pa3gsb/Radioberry-2.x-extensions/Radioberry_LPF_V1.3/Radioberry_LPF_V1.3/3D_ models/WE_7845.stp

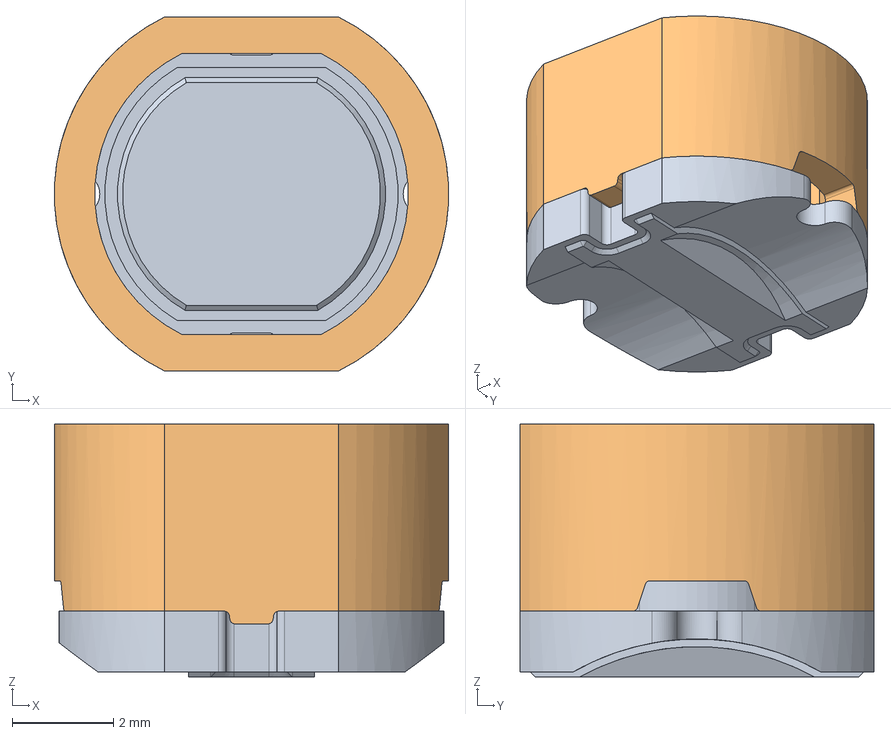
[picture p23: CAD file, 2020-11-24]
Radioberry_LPF_V1.3/Radioberry_LPF_V1.3/3D_ models/WE_7845.stp
7.79 x 7.00 x 5.00 mm
