pa3gsb/Radioberry-2.x-extensions/Radioberry-PA-20W/3D_Models/CAP2200_n.STEP

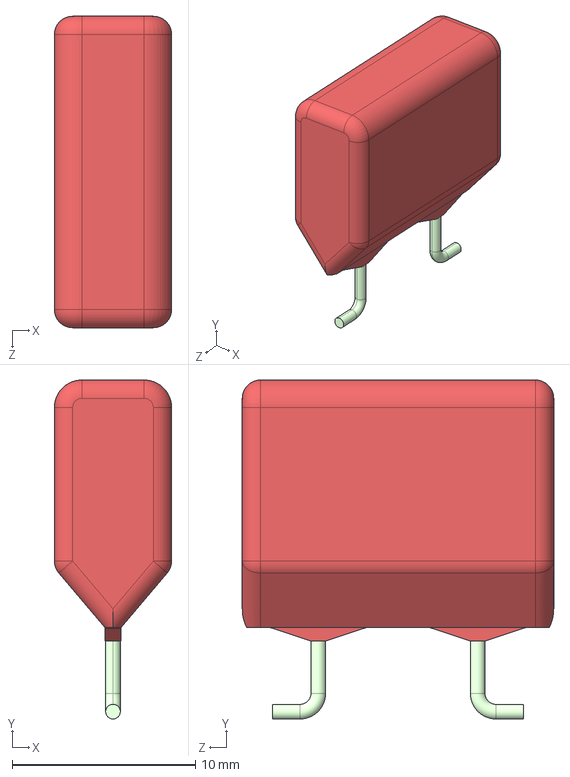
[picture p24: CAD file, 2020-11-24]
Radioberry-PA-20W/3D_Models/CAP2200_n.STEP
6.40 x 18.5 x 17.0 mm
