pa3gsb/Radioberry-2.x-extensions/Radioberry_LPF_V1.3/Radioberry_LPF_V1.3/3D_ models/AGQ_(GQ)_Relays.STEP

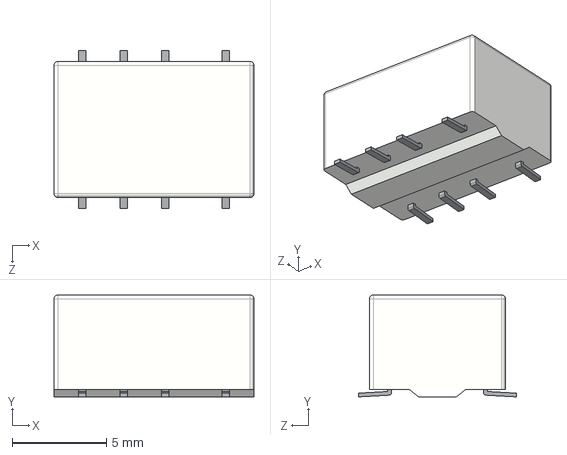
[picture p25: CAD file, 2020-11-24]
Radioberry_LPF_V1.3/Radioberry_LPF_V1.3/3D_ models/AGQ_(GQ)_Relays.STEP
10.6 x 5.40 x 8.40 mm
