pa3gsb/Radioberry-2.x-extensions/Radioberry-PA-20W/3D_Models/PJ-063BH.step

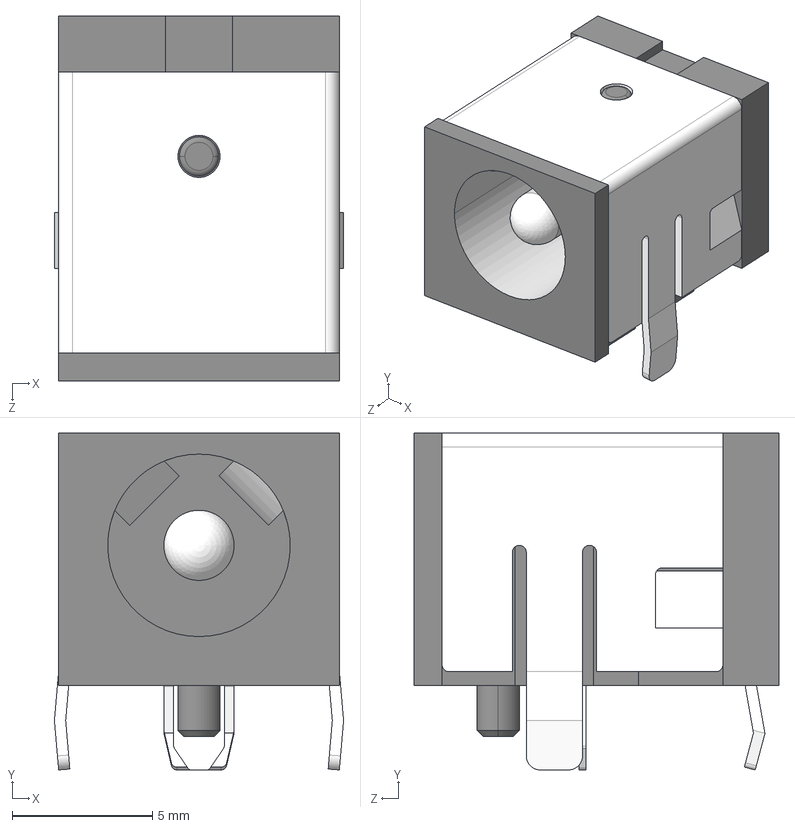
[picture p26: CAD file, 2020-11-24]
Radioberry-PA-20W/3D_Models/PJ-063BH.step
10.3 x 12.0 x 13.0 mm
