pa3gsb/Radioberry-2.x-extensions/Radioberry_LPF_V1.3/Radioberry_LPF_V1.3/3D_ models/sma1.STEP

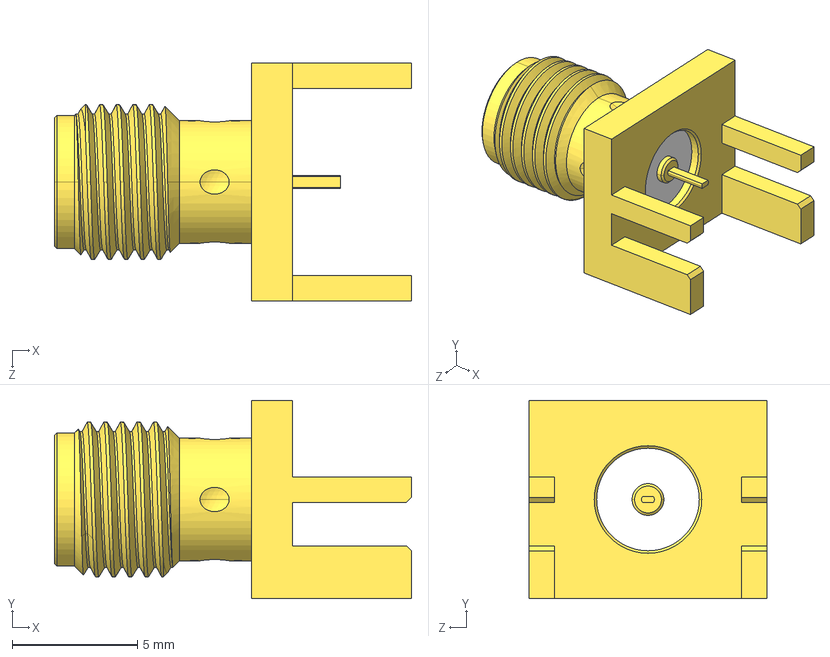
[picture p27: CAD file, 2020-11-24]
Radioberry_LPF_V1.3/Radioberry_LPF_V1.3/3D_ models/sma1.STEP
14.3 x 7.92 x 9.52 mm
