pa3gsb/Radioberry-2.x-extensions/Radioberry-PA-20W/3D_Models/CAP2200.STEP

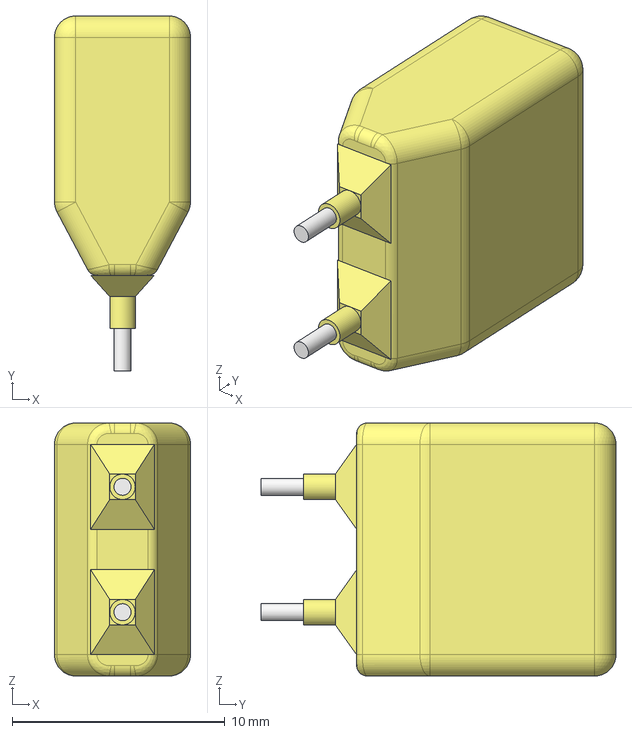
[picture p28: CAD file, 2020-11-24]
Radioberry-PA-20W/3D_Models/CAP2200.STEP
6.40 x 16.7 x 11.9 mm
