pa3gsb/Radioberry-2.x-extensions/Radioberry-PA-20W/3D_Models/SMA-J-P-H-RA-TH1.stp

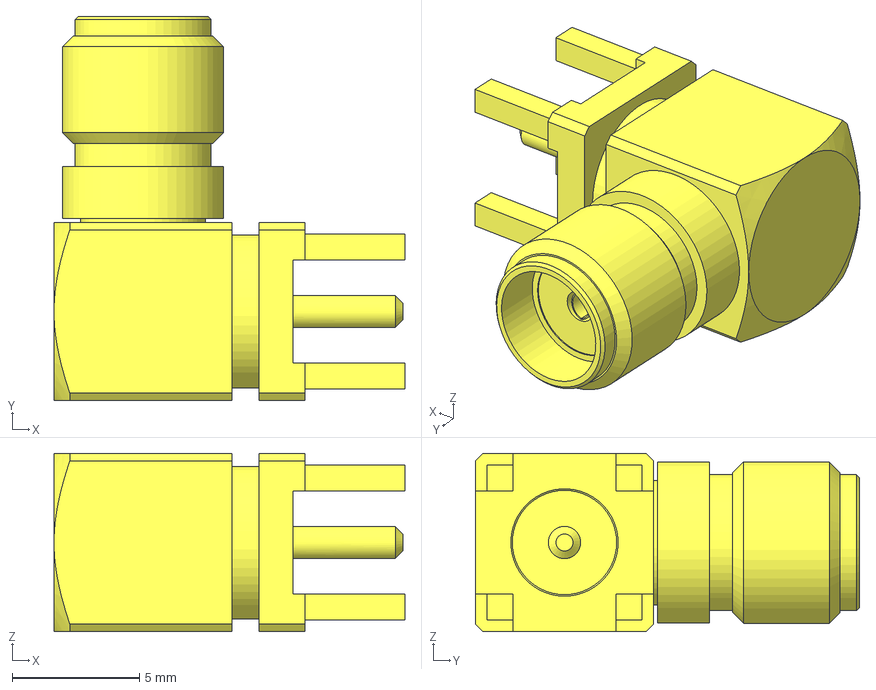
[picture p29: CAD file, 2020-04-24]
Radioberry-PA-20W/3D_Models/SMA-J-P-H-RA-TH1.stp
13.8 x 15.1 x 7.00 mm
