pa3gsb/Radioberry-2.x-extensions/Radioberry_LPF_V1.3/Radioberry_LPF_V1.3/3D_ models/SN74LVC1G34DBVR.STEP

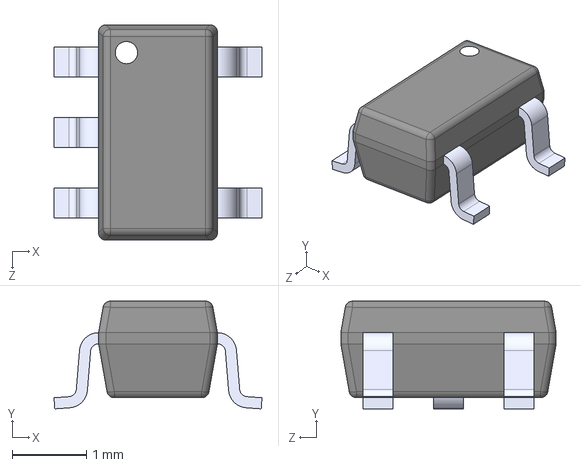
[picture p30: CAD file, 2020-11-24]
Radioberry_LPF_V1.3/Radioberry_LPF_V1.3/3D_ models/SN74LVC1G34DBVR.STEP
2.80 x 1.45 x 2.90 mm
