pa3gsb/Radioberry-2.x-extensions/Radioberry-PA-20W/3D_Models/to92SMD.STEP

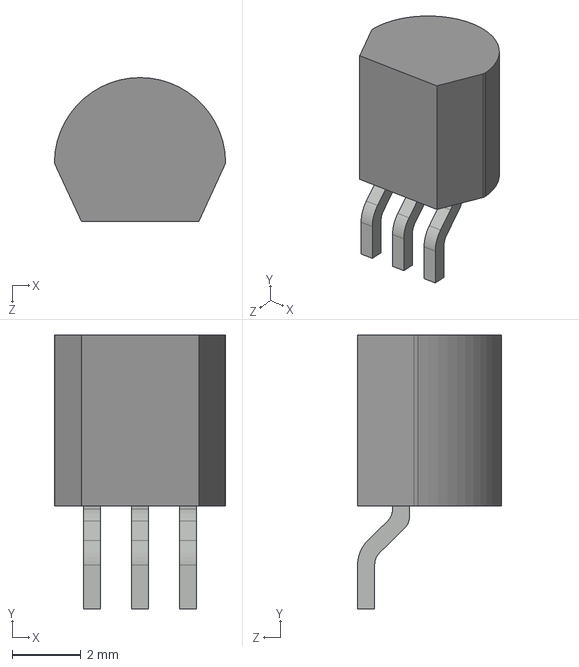
[picture p31: CAD file, 2020-04-24]
Radioberry-PA-20W/3D_Models/to92SMD.STEP
5.00 x 8.00 x 4.20 mm
TO92
to92pin x 3
