pa3gsb/Radioberry-2.x-extensions/Radioberry_LPF_V1.3/Radioberry_LPF_V1.3/3D_ models/SRP2510A.stp

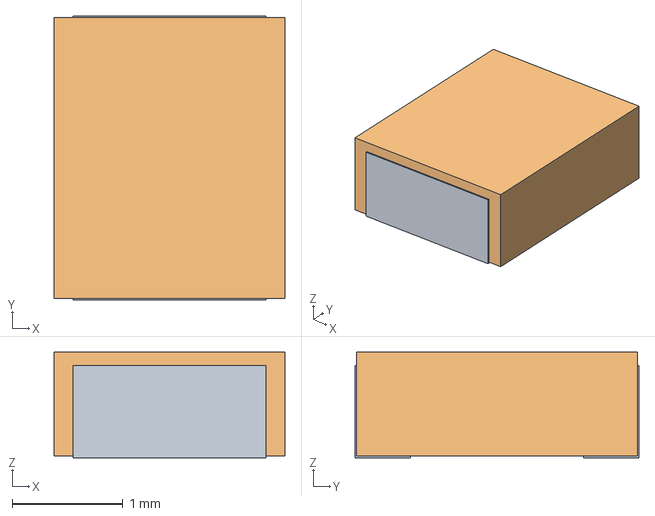
[picture p32: CAD file, 2020-11-24]
Radioberry_LPF_V1.3/Radioberry_LPF_V1.3/3D_ models/SRP2510A.stp
2.09 x 2.57 x 0.955 mm
