pa3gsb/Radioberry-2.x-extensions/Radioberry-PA-20W/3D_Models/BN43-1502.STEP

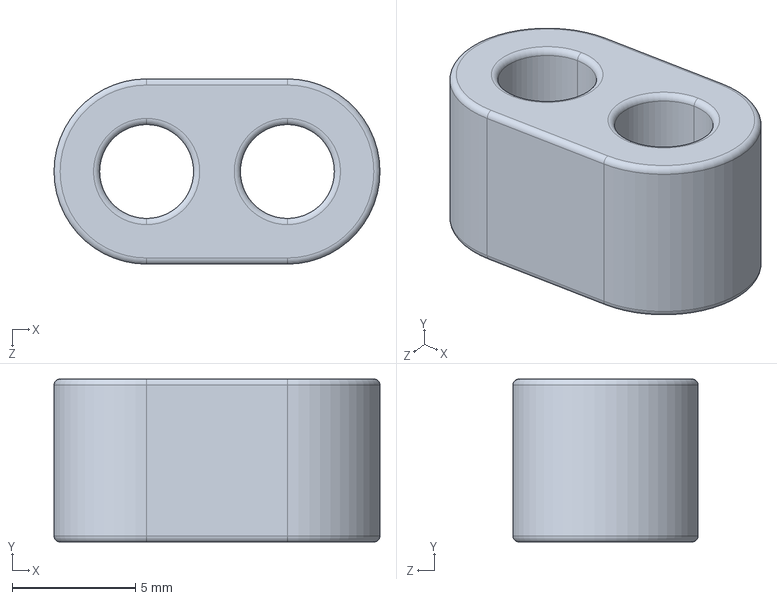
[picture p33: CAD file, 2020-04-24]
Radioberry-PA-20W/3D_Models/BN43-1502.STEP
13.2 x 6.60 x 7.50 mm
