pa3gsb/Radioberry-2.x-extensions/Radioberry-PA-20W/3D_Models/BN43-2402.STEP

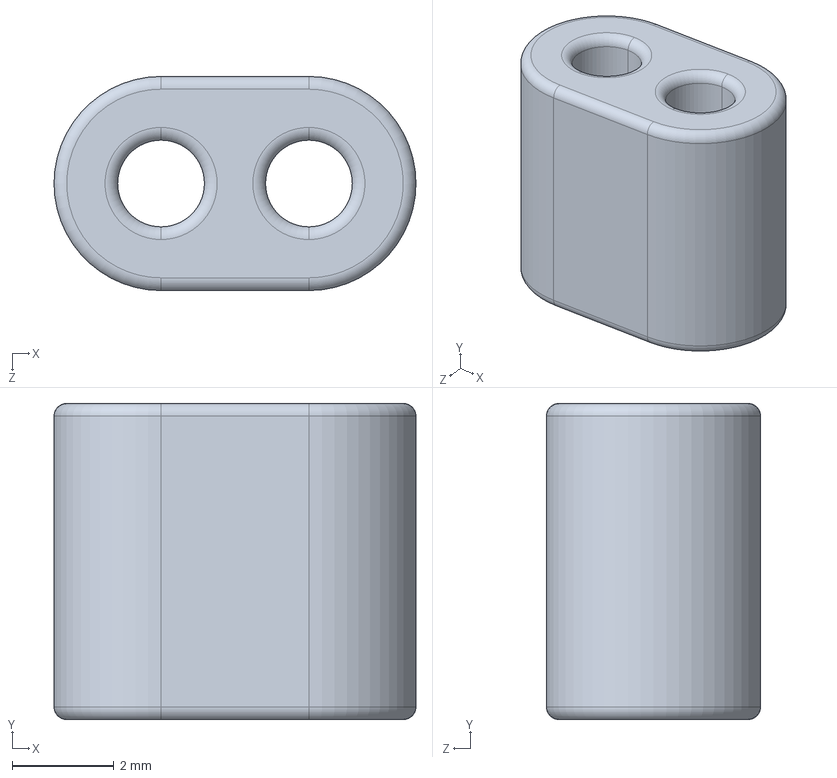
[picture p35: CAD file, 2020-04-24]
Radioberry-PA-20W/3D_Models/BN43-2402.STEP
7.10 x 6.20 x 4.20 mm
