pa3gsb/Radioberry-2.x-extensions/Radioberry-PA-20W/3D_Models/EDH106M025A9BAA.step

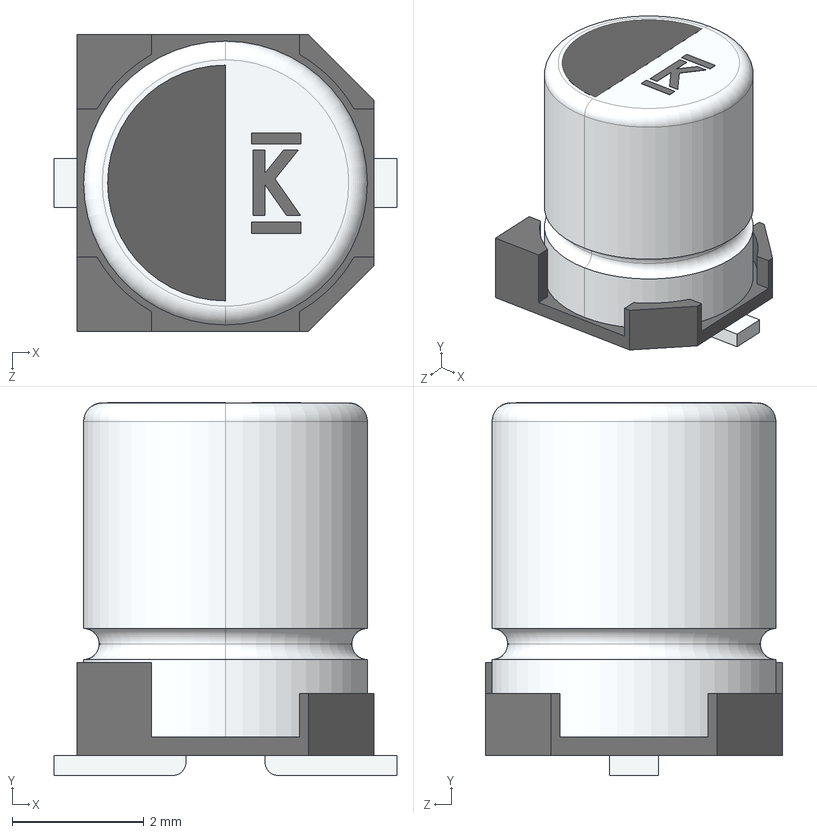
[picture p37: CAD file, 2020-04-24]
Radioberry-PA-20W/3D_Models/EDH106M025A9BAA.step
5.20 x 5.66 x 4.50 mm
