pa3gsb/Radioberry-2.x-extensions/Radioberry-PA-20W/3D_Models/BN43-202.STEP

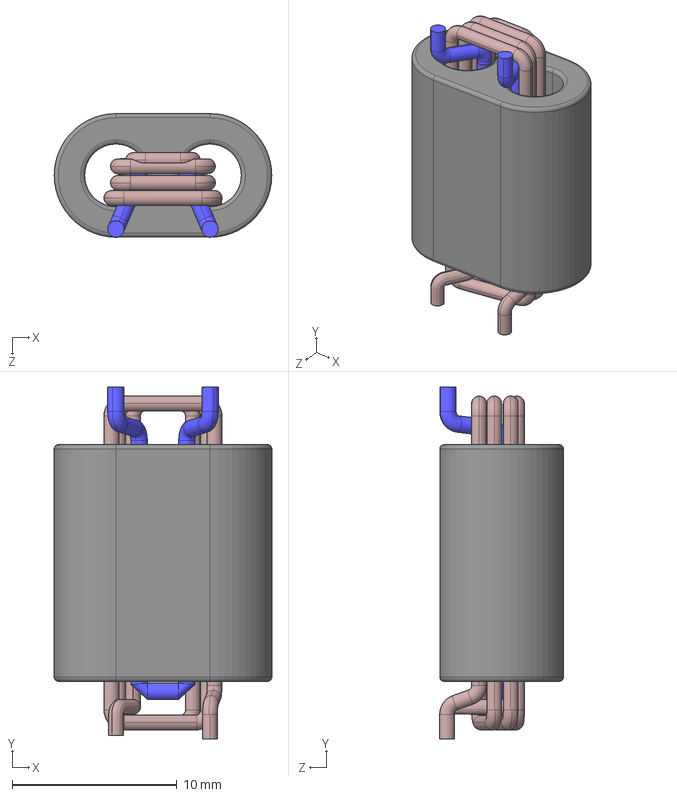
[picture p39: CAD file, 2020-04-24]
Radioberry-PA-20W/3D_Models/BN43-202.STEP
13.2 x 21.4 x 7.51 mm
BN43-202
primary
pin x 2
secondary
