pa3gsb/Radioberry-2.x-extensions/Radioberry_LPF_V1.3/Radioberry_LPF_V1.3/3D_ models/SRN6028 series.stp

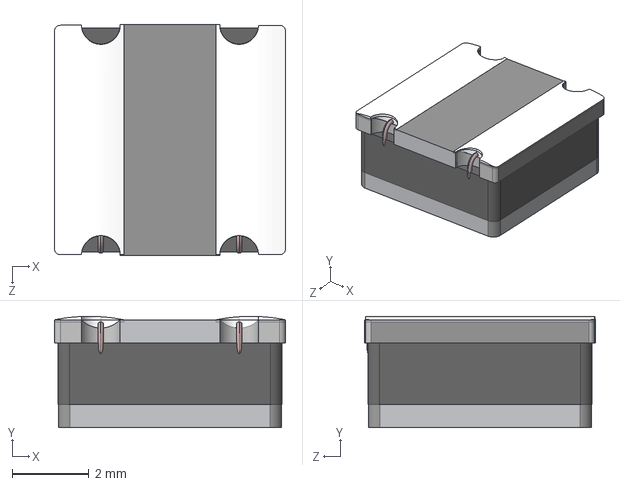
[picture p41: CAD file, 2020-11-24]
Radioberry_LPF_V1.3/Radioberry_LPF_V1.3/3D_ models/SRN6028 series.stp
6.00 x 2.89 x 6.00 mm
