pa3gsb/Radioberry-2.x-extensions/Radioberry_LPF_V1.3/Radioberry_LPF_V1.3/3D_ models/IND_NLCV32TR_TDK.step

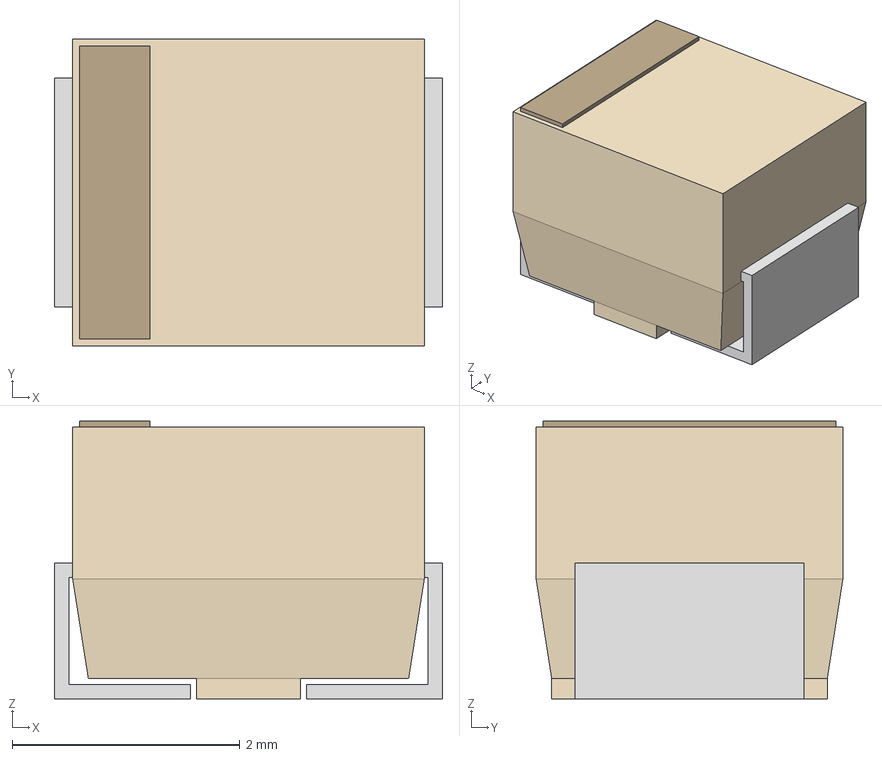
[picture p42: CAD file, 2020-11-24]
Radioberry_LPF_V1.3/Radioberry_LPF_V1.3/3D_ models/IND_NLCV32TR_TDK.step
3.40 x 2.69 x 2.44 mm
