pa3gsb/Radioberry-2.x-extensions/Radioberry_LPF_V1.3/Radioberry_LPF_V1.3/3D_ models/WE_7440450018.stp

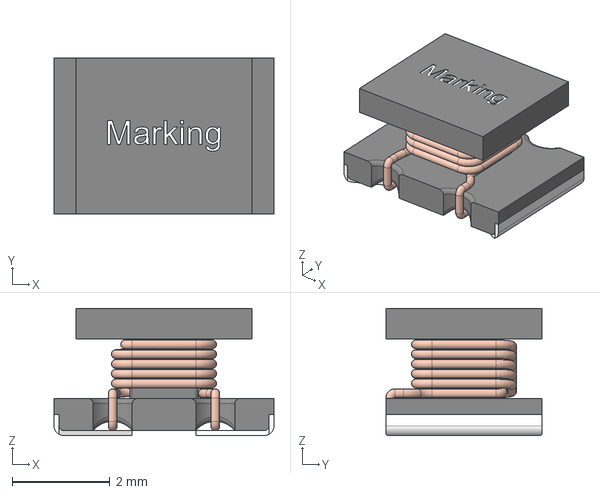
[picture p43: CAD file, 2020-11-24]
Radioberry_LPF_V1.3/Radioberry_LPF_V1.3/3D_ models/WE_7440450018.stp
4.50 x 3.20 x 2.60 mm
Kern x 2
Pin x 2
