pa3gsb/Radioberry-2.x-extensions/Radioberry_LPF_V1.3/Radioberry_LPF_V1.3/3D_ models/SRN2012 series.stp

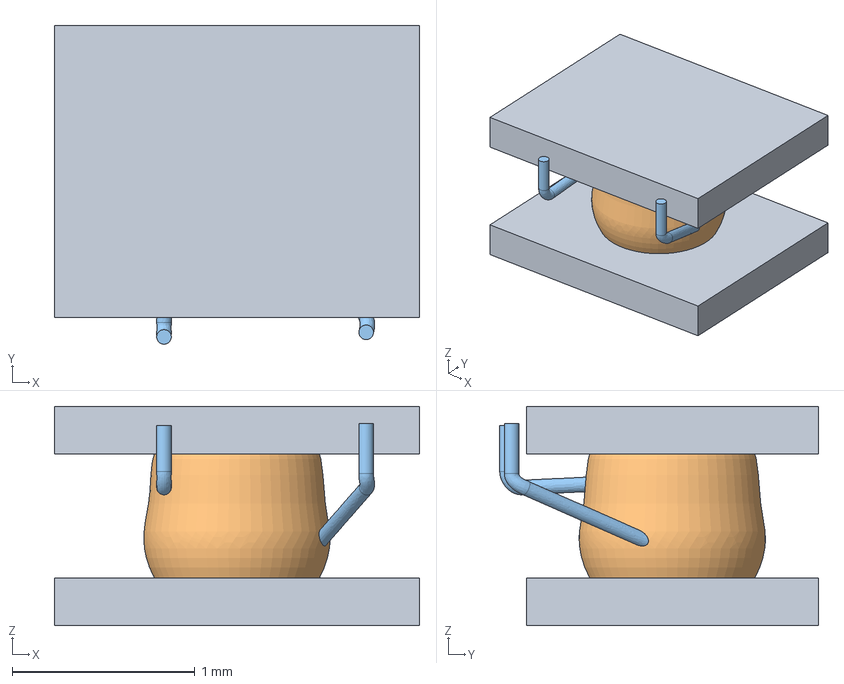
[picture p44: CAD file, 2020-11-24]
Radioberry_LPF_V1.3/Radioberry_LPF_V1.3/3D_ models/SRN2012 series.stp
2.00 x 1.75 x 1.20 mm
